MOSH-Insa-Toulouse/2023-2024-4GP-TLILI-SISTEEDHUR/Images/APKlike/FlexiGraphite1024.png

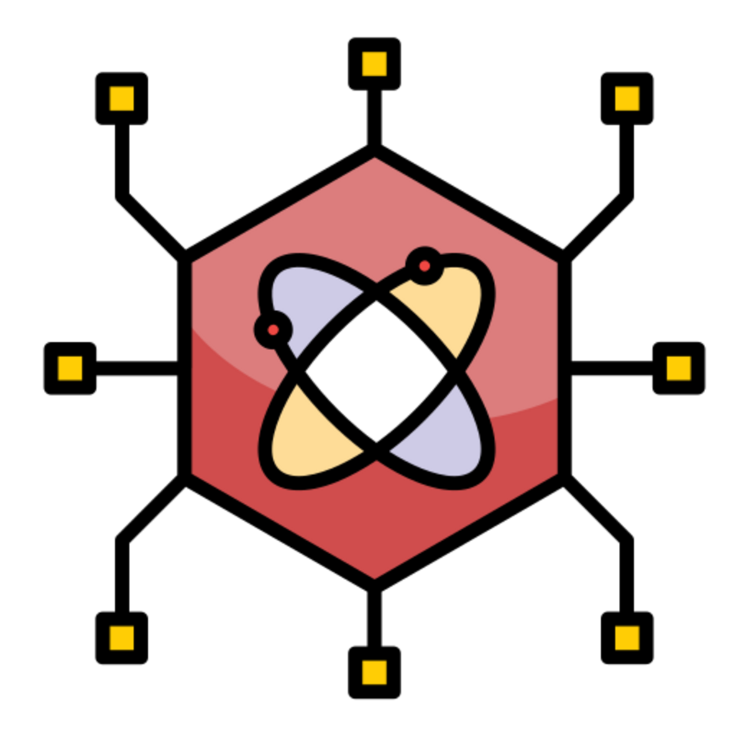
Images/APKlike/FlexiGraphite1024.png
