MOSH-Insa-Toulouse/2023-2024-4GP-TLILI-SISTEEDHUR/Images/APKlike/Menu FlexiGraphite.jpg

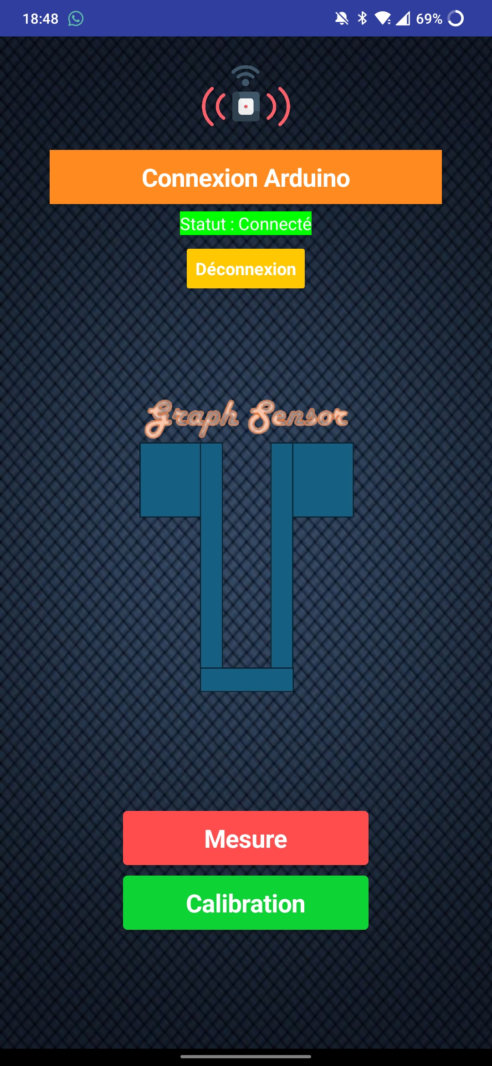
Images/APKlike/Menu FlexiGraphite.jpg
