MOSH-Insa-Toulouse/2023-2024-4GP-TLILI-SISTEEDHUR/Images/APKlike/Symbol Graph Sensor.png

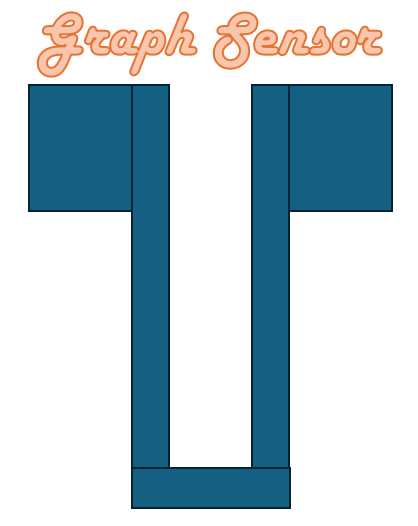
Images/APKlike/Symbol Graph Sensor.png
