MOSH-Insa-Toulouse/2023-2024-4GP-TLILI-SISTEEDHUR/Images/Kicad/3DView/Top view.png

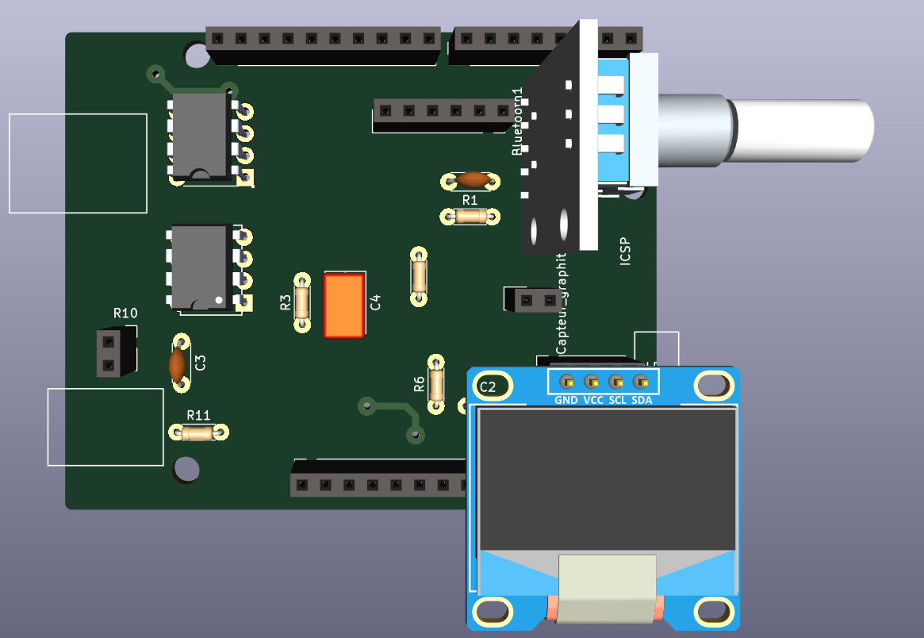
Images/Kicad/3DView/Top view.png
