MOSH-Insa-Toulouse/2023-2024-4GP-TLILI-SISTEEDHUR/Images/Kicad/Amplificateur transimpédance Symbol.png

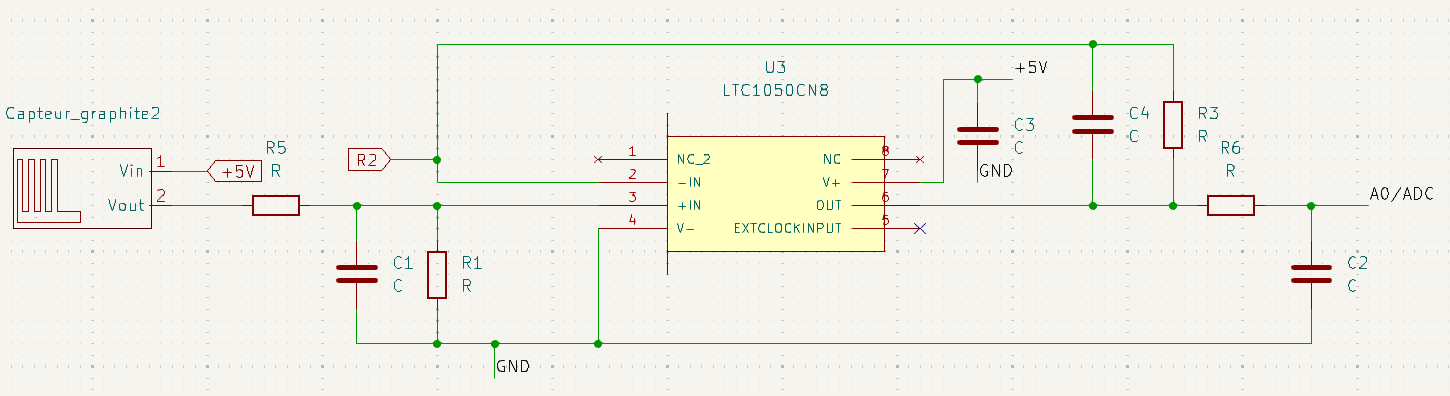
Images/Kicad/Amplificateur transimpédance Symbol.png
