MOSH-Insa-Toulouse/2023-2024-4GP-TLILI-SISTEEDHUR/Images/Kicad/Capteur Graphite footprint.png

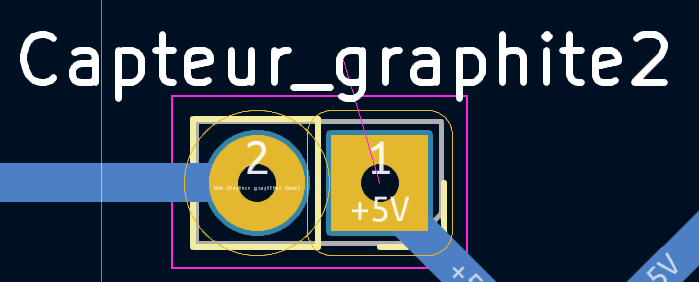
Images/Kicad/Capteur Graphite footprint.png
