MOSH-Insa-Toulouse/2023-2024-4GP-TLILI-SISTEEDHUR/Images/Kicad/Capteur Graphite Symbol.png

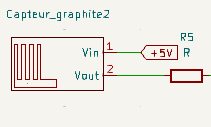
Images/Kicad/Capteur Graphite Symbol.png
