MOSH-Insa-Toulouse/2023-2024-4GP-TLILI-SISTEEDHUR/Images/Kicad/Flexsensor footprint.png

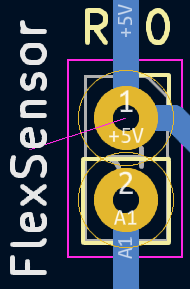
Images/Kicad/Flexsensor footprint.png
