MOSH-Insa-Toulouse/2023-2024-4GP-TLILI-SISTEEDHUR/Images/Kicad/Flexsensor Symbol.png

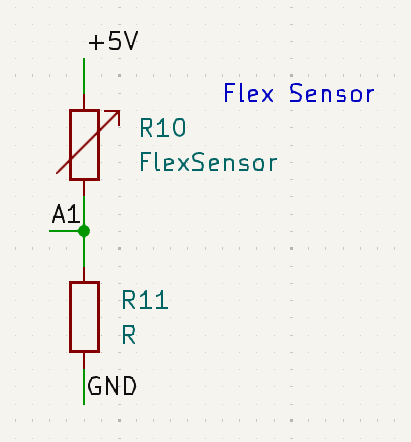
Images/Kicad/Flexsensor Symbol.png
