MOSH-Insa-Toulouse/2023-2024-4GP-TLILI-SISTEEDHUR/Images/Kicad/KY-040 Symbol.png

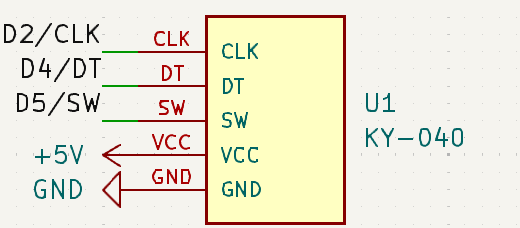
Images/Kicad/KY-040 Symbol.png
