MOSH-Insa-Toulouse/2023-2024-4GP-TLILI-SISTEEDHUR/Images/Kicad/LTC 1050 footprint.png

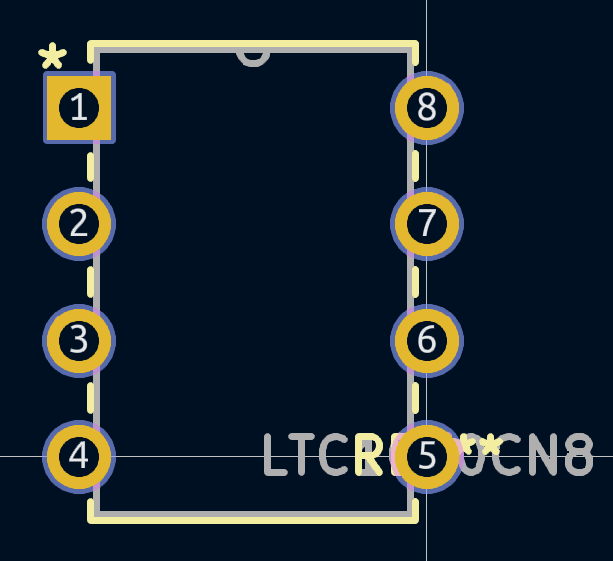
Images/Kicad/LTC 1050 footprint.png
