MOSH-Insa-Toulouse/2023-2024-4GP-TLILI-SISTEEDHUR/Images/Kicad/MPC41050 Symbol.png

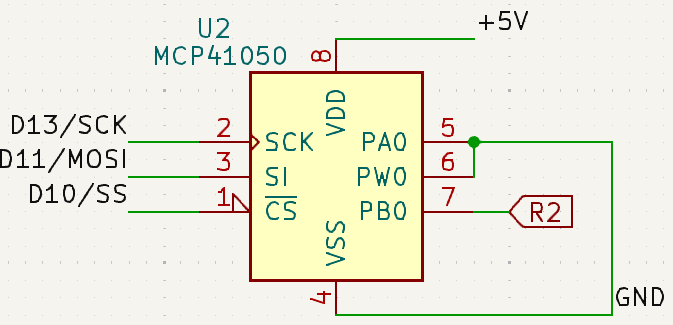
Images/Kicad/MPC41050 Symbol.png
