MOSH-Insa-Toulouse/2023-2024-4GP-TLILI-SISTEEDHUR/Images/Kicad/OLED Screen Symbol.png

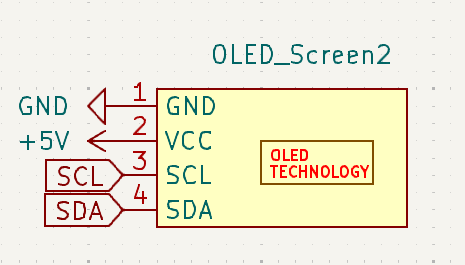
Images/Kicad/OLED Screen Symbol.png
