MOSH-Insa-Toulouse/2023-2024-4GP-TLILI-SISTEEDHUR/Images/Kicad/PCB1.png

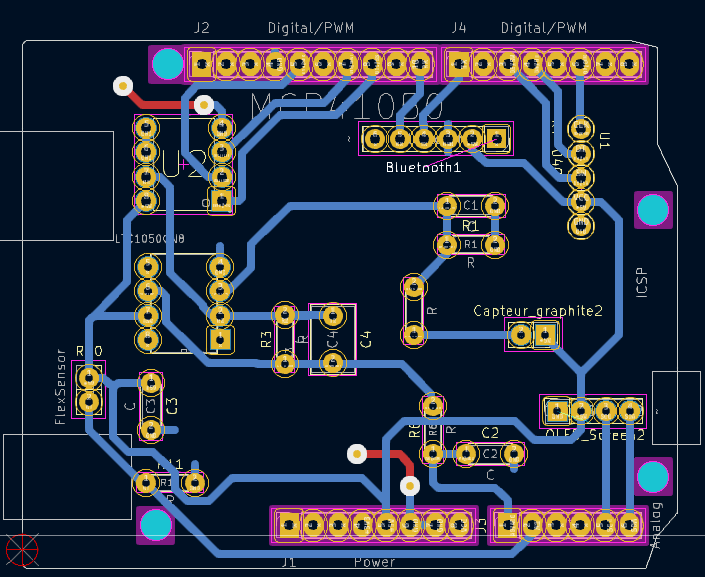
Images/Kicad/PCB1.png
