MOSH-Insa-Toulouse/2023-2024-4GP-TLILI-SISTEEDHUR/Images/Kicad/PCB2.png

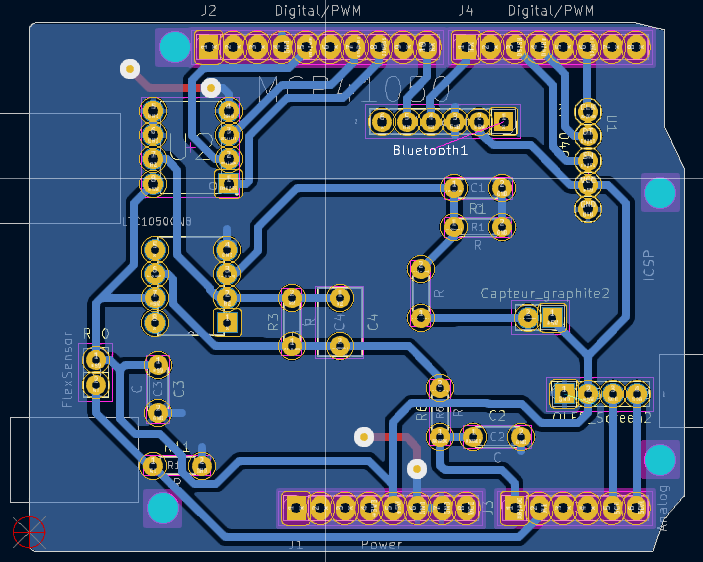
Images/Kicad/PCB2.png
