MOSH-Insa-Toulouse/2023-2024-4GP-TLILI-SISTEEDHUR/Images/LTSpice/Circuit LTSpice.png

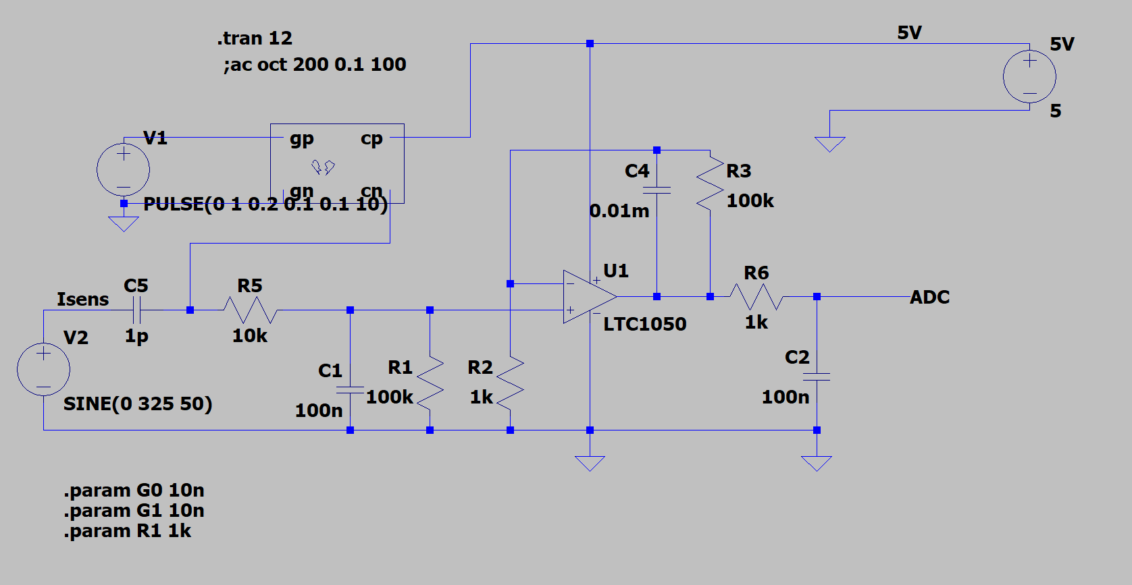
Images/LTSpice/Circuit LTSpice.png
