MOSH-Insa-Toulouse/2023-2024-4GP-TLILI-SISTEEDHUR/Images/PCB/Masque PCB.png

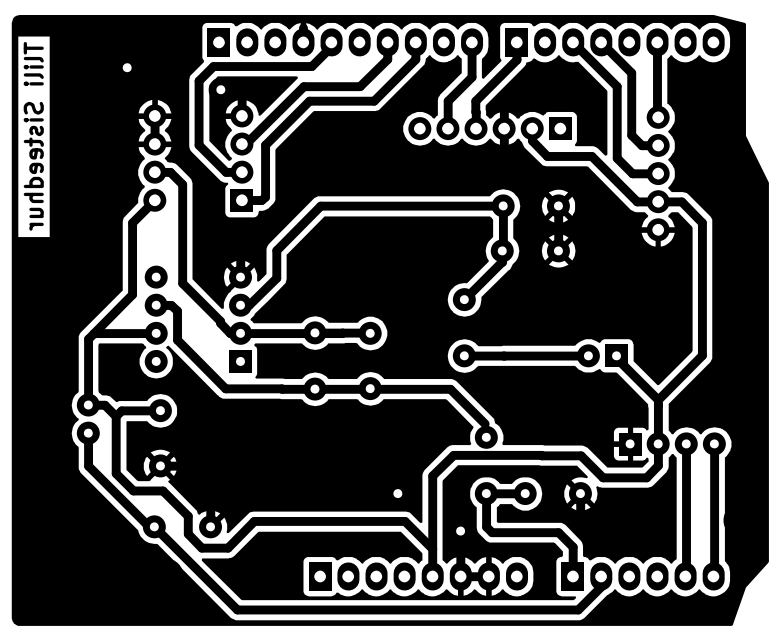
Images/PCB/Masque PCB.png
