MOSH-Insa-Toulouse/2023-2024-4GP-TLILI-SISTEEDHUR/Images/PCB/Shield1.jpg

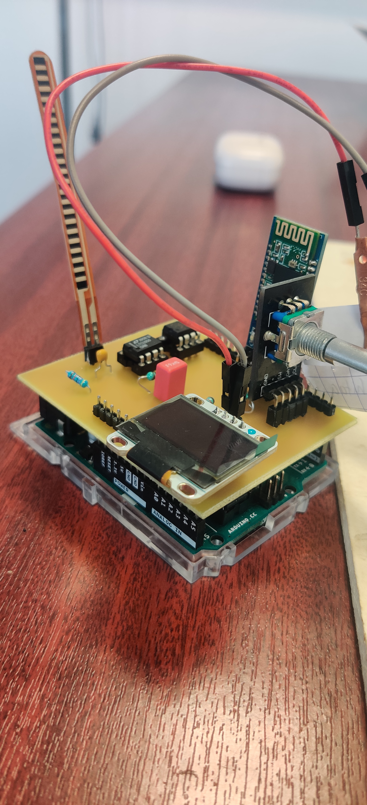
Images/PCB/Shield1.jpg
