MOSH-Insa-Toulouse/2023-2024-4GP-TLILI-SISTEEDHUR/Images/Banc de test/deformation en compression.png

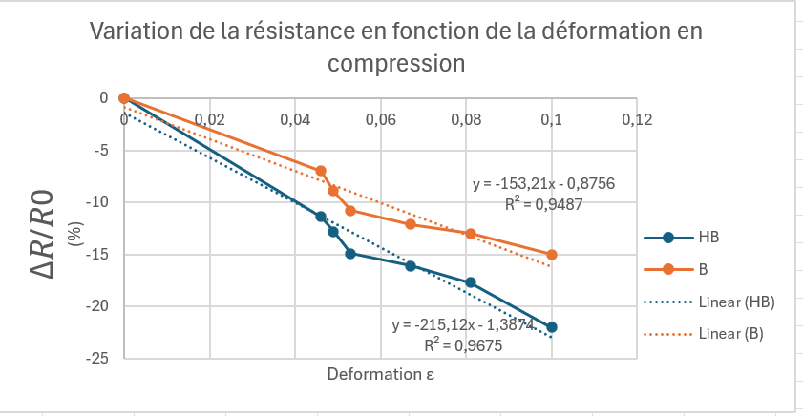
Images/Banc de test/deformation en compression.png
