MOSH-Insa-Toulouse/2023-2024-4GP-TLILI-SISTEEDHUR/Images/Banc de test/Deformation flexsensor.png

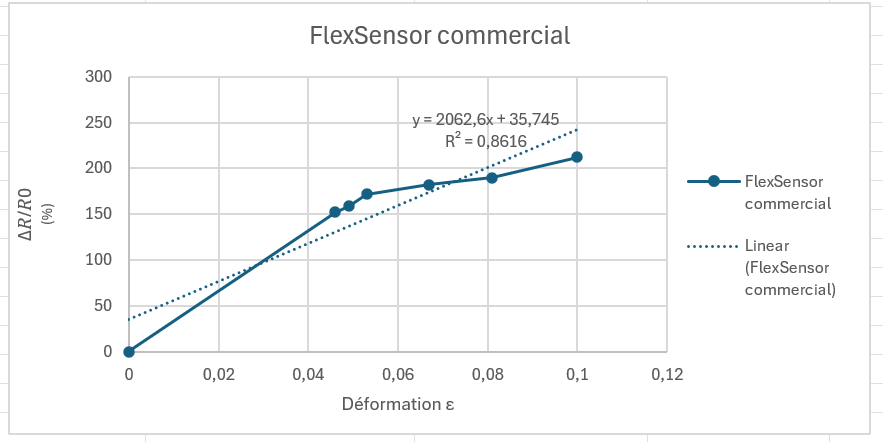
Images/Banc de test/Deformation flexsensor.png
