MOSH-Insa-Toulouse/2023-2024-4GP-TLILI-SISTEEDHUR/Images/Banc de test/Déformation en tension.png

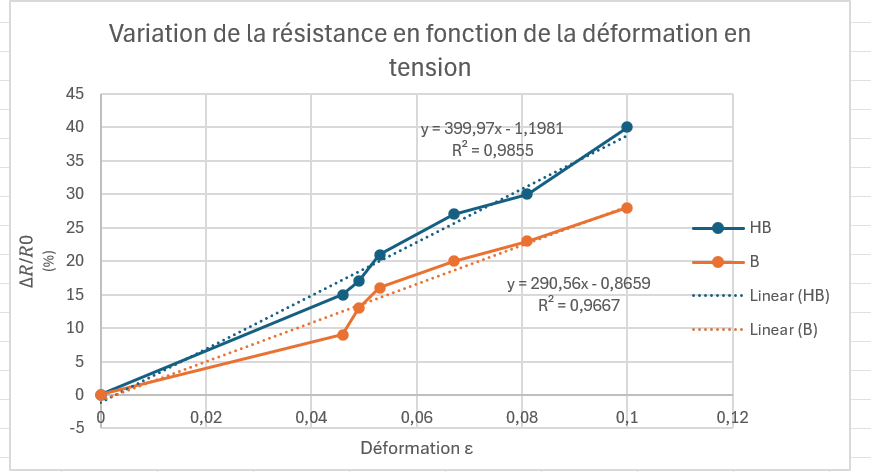
Images/Banc de test/Déformation en tension.png
